DucaRaresAndrei/EBook-Reader/Images/Display.png

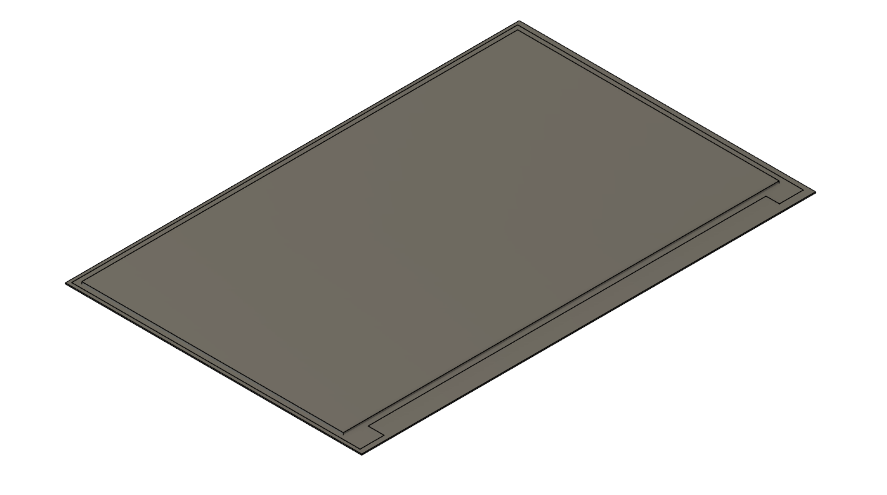
Images/Display.png
